enricocirignaco/berry_case/firmware/python/globals.py

# Project:   berry_case
# File:      globals.py
# Autor:     Enrico Cirignaco
# Created:   29.11.2020

# Import modules
#############################################################################

menu_depth = 0
main_menu_entry = 0
network_menu_entry = 0
system_info_menu_entry = 0
is_display_on = False
display_counter = 0
is_fan_auto_enabled = True
fan_speed_man = 1
